jasonluther/bocce/img/first-border-course.jpg

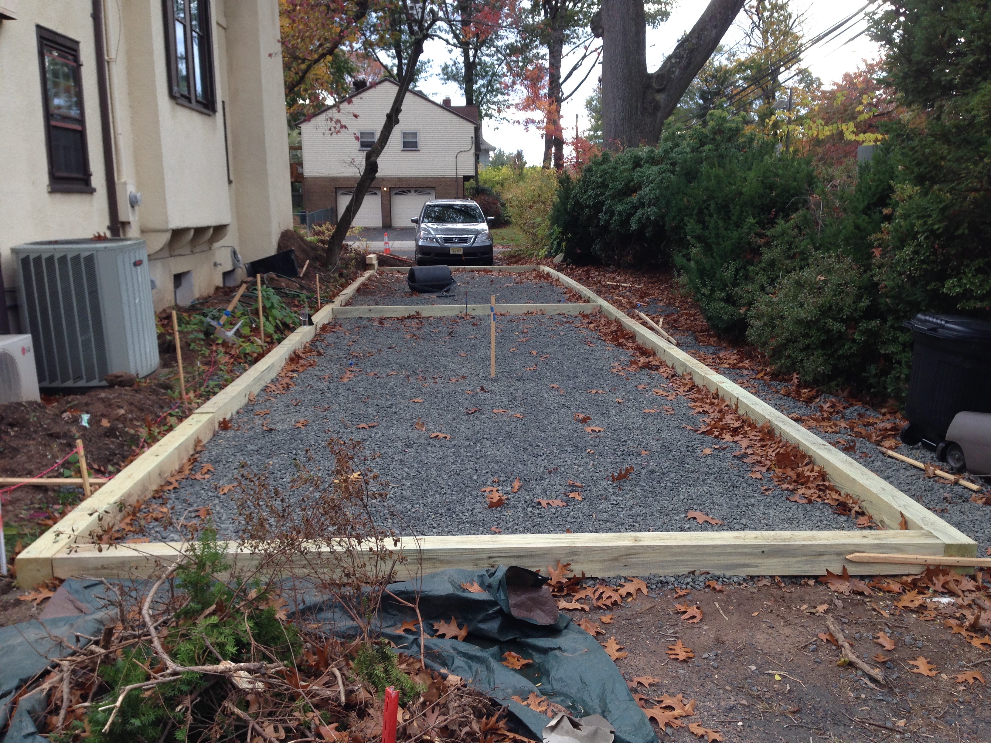
img/first-border-course.jpg
